gordondan/dupont-clip/generated/DupontClip_8way_p1-4_2.54mm_2.5x2.2x14_Clip.stl

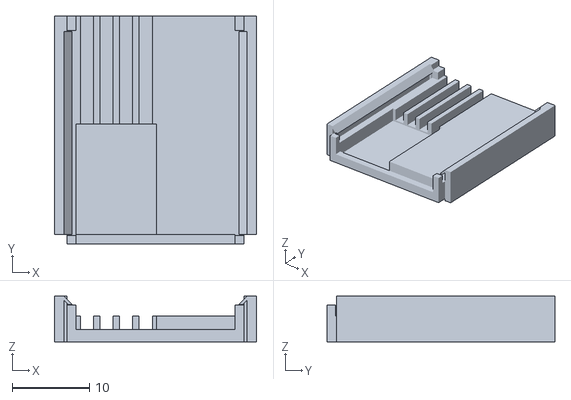
[picture p15: CAD file, 2026-08-12]
generated/DupontClip_8way_p1-4_2.54mm_2.5x2.2x14_Clip.stl
26.2 x 29.5 x 5.90
