gordondan/dupont-clip/generated/DupontClip_4way_all_2.54mm_2.54x2.54x14_Lid.stl

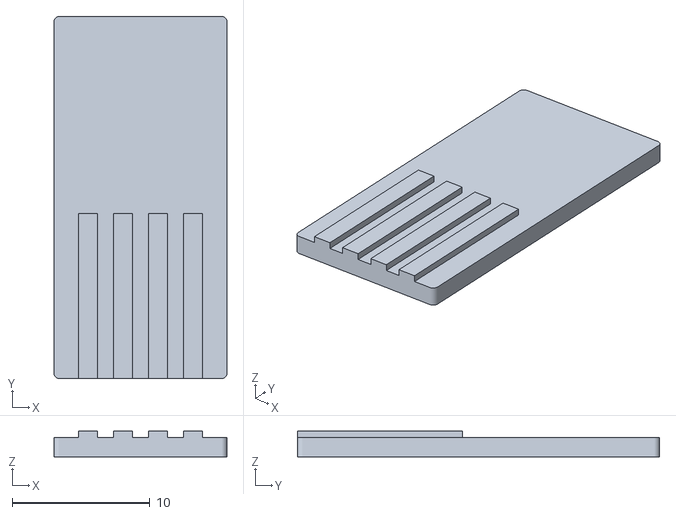
[picture p16: CAD file, 2026-08-12]
generated/DupontClip_4way_all_2.54mm_2.54x2.54x14_Lid.stl
12.6 x 26.3 x 1.87
